AmarS03/Tiny-Parking-System/3d-print-model/images/3.png

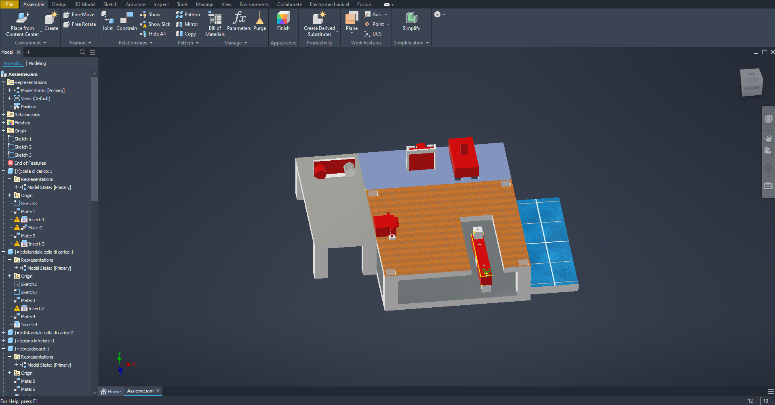
3d-print-model/images/3.png
