AmarS03/Tiny-Parking-System/esp/components/ultrasonic_sensor/ultrasonic_sensor.h

/**
 * @file ultrasonic.h
 * 
 * Header file for the ultrasonic sensor interface module
 * 
 */

#ifndef ULTRASONIC_SENSOR_H
#define ULTRASONIC_SENSOR_H

#include "esp_err.h"
#include <stdbool.h>

esp_err_t ultrasonic_sensor_init();

bool ultrasonic_sensor_detect();

#endif /* ULTRASONIC_SENSOR_H */
