AmarS03/Tiny-Parking-System/esp/main/fsm.c

/*
 * fsm.c
 *
 * Function definitions for the various states of the system
 *
 */

#include "fsm.h"
#include "freertos/FreeRTOS.h"
#include "freertos/task.h"
#include "freertos/event_groups.h"
#include "driver/gpio.h"
#include "ultrasonic.h"
#include "esp_wifi.h"
#include "esp_event.h"
#include "esp_log.h"
#include "esp_system.h"
#include "esp_sleep.h"

#include <stdbool.h>

#include "../components/cv/cv.h"
#include "../components/weight/weight.h"
#include "../components/ultrasonic_sensor/ultrasonic_sensor.h"
#include "../components/https/https.h"
#include "../components/https/https_task.h"
#include "../components/init/init.h"
#include "../components/servo_motor/servo_motor.h"
#include "../components/oled/oled.h"

// Idle delay function for low power mode
#ifdef CONFIG_USE_MOCK_CAMERA
    #define IDLE_DELAY() vTaskDelay(pdMS_TO_TICKS(200))
#else
    #define IDLE_DELAY() do { \
        esp_sleep_enable_timer_wakeup(200000); \
        esp_light_sleep_start(); \
    } while(0)
#endif

#define TOTAL_PARKING_SPOTS 10

// Current state of the FSM
static State_t curr_state = INIT;

// Flag that avoids multiple concurrent recognitions
static bool recognition_busy = false;

// Parking spot counter
static int parking_spots_available = TOTAL_PARKING_SPOTS;

// Prototypes of state functions
static void init_fn();

static void idle_fn();

static void entry_fn();

static void refuse_fn();

static void allow_fn();

static void exit_fn();


////////////////////////////////////////////////////////////////
//////////////// FSM Logic /////////////////////////////////////
////////////////////////////////////////////////////////////////

void fsm_handle_event(Event_t event) {
    switch (curr_state) {
        case IDLE:
            if (event == VALID_WEIGHT_DETECTED) {
                curr_state = VEHICLE_ENTRY;
            } else if (event == EXIT_DETECTED) {
                curr_state = VEHICLE_EXIT;
            } else if (event == REMOTE_OPEN) {
                curr_state = ENTRY_ALLOWED;
            }
            break;
        case VEHICLE_ENTRY:
            if (event == PLATE_RECOGNIZED) {
                curr_state = ENTRY_ALLOWED;
            } else if (event == PLATE_REFUSED) {
                curr_state = ENTRY_REFUSED;
            }
            break;
        default:
            // Handle invalid state
        break;
    }

}

void fsm_run_state_function() {
    switch (curr_state) {
        case INIT:
            init_fn();
            break;
        case IDLE:
            idle_fn();
            break;
        case VEHICLE_ENTRY:
            entry_fn();
            break;
        case ENTRY_REFUSED:
            refuse_fn();
            break;
        case ENTRY_ALLOWED:
            allow_fn();
            break;
        case VEHICLE_EXIT:
            exit_fn();
            break;
        default:
            // Handle invalid state
            break;
    }
}

////////////////////////////////////////////////////////////////
//////////////// FSM State Functions ///////////////////////////
////////////////////////////////////////////////////////////////

/**
 * Initializes the whole system
 */
void init_fn() {
    system_init();

    #ifdef CONFIG_USE_MOCK_CAMERA
    ESP_LOGI("IDLE", "Running in MOCK CAMERA mode (Wokwi simulation)");
    #endif

    ESP_LOGI("INIT", "System ready. Waiting for detection...");

    vTaskDelay(pdMS_TO_TICKS(2000));

    ESP_LOGI("INIT", "Displaying status on OLED...");


    oled_print(0, "ESP32-S3 READY");
    oled_print(2, "HX711 OK");
    oled_print(4, "WiFi CONNECTED");

    vTaskDelay(pdMS_TO_TICKS(5000));

    oled_clear();

    curr_state = IDLE;
}

/**
 * When in idle state, the system enters low
 * power mode and waits for interrupts
 */
void idle_fn() {
    // System waiting for an event
    oled_clear();

    if (parking_spots_available <= 0) {
        enable_weight_detection(false);
        oled_print(2, "The parking lot");
        oled_print(4, "is full!");
    } else {
        enable_weight_detection(true);
        recognition_busy = false;
        char spots_str[20];
        snprintf(spots_str, sizeof(spots_str), "%d parking spots", parking_spots_available);
        oled_print(2, spots_str);
        oled_print(4, "available");
    }

    // Enter low power mode
    IDLE_DELAY();

    // wait for the ultrasonic sensor to detect vehicle passage
    if (ultrasonic_sensor_detect()) {
        ESP_LOGI("IDLE", "Detected vehicle exiting...");
        vTaskDelay(pdMS_TO_TICKS(500)); // Debounce delay
        fsm_handle_event(EXIT_DETECTED);
    }
}

/**
 * Detects weight and runs the CV algorithm.
 * Decide whether to allow or refuse entrance
 */
void entry_fn() {
    enable_weight_detection(false);

    oled_clear();

    oled_print(2, "Verifying license");
    oled_print(4, "plate...");

    if (!recognition_busy) {
        unblock_recognition_task();
        recognition_busy = true;
    }

    vTaskDelay(pdMS_TO_TICKS(2000));

    oled_clear();
}

/**
 * Shows a negative message
 * on the display
 */
void refuse_fn() {
    oled_clear();
    ESP_LOGI("REFUSE", "Entry refused. Access denied.");

    oled_print(2, "Your vehicle");
    oled_print(4, "is not allowed!");

    vTaskDelay(pdMS_TO_TICKS(5000));

    oled_clear();
    curr_state = IDLE;
}

/**
 * Shows a positive message on the
 * display, opens the gate bar and waits a signal
 * from the ultrasonic sensor to close it again
 */
void allow_fn() {
    oled_clear();
    ESP_LOGI("ALLOW", "Entry allowed. Opening gate...");

    oled_print(3, "Entrance allowed!");

    // Update counter
    parking_spots_available -= (parking_spots_available > 1) ? 1 : 0;

    // raise the barrier when entry is allowed
    servo_motor_raise_barrier();

    // wait for the ultrasonic sensor to detect vehicle passage
    bool is_still_detecting = false;

    // Await vehicle passage
    while (!is_still_detecting) {
        is_still_detecting = ultrasonic_sensor_detect();
        vTaskDelay(pdMS_TO_TICKS(200));
    }

    ESP_LOGI("ALLOW", "Vehicle passing the gate...");

    // Await vehicle clearance
    while (is_still_detecting) {
        is_still_detecting = ultrasonic_sensor_detect();
        vTaskDelay(pdMS_TO_TICKS(200));
    }

    ESP_LOGI("ALLOW", "Vehicle passed. Closing gate...");

    oled_clear();

    oled_print(3, "Closing gate...");
    
    // close the barrier after ultrasonic read
    servo_motor_lower_barrier();
    vTaskDelay(pdMS_TO_TICKS(3000));
    
    oled_clear();
    curr_state = IDLE;
}

/**
 * Opens the gate bar for exit
 * and waits for the vehicle to leave
 */
void exit_fn() {
    oled_clear();
    enable_weight_detection(false);
    ESP_LOGI("EXIT", "Exit allowed. Opening gate...");

    oled_print(3, "Vehicle exiting");

    // Update counter
    parking_spots_available += (parking_spots_available < TOTAL_PARKING_SPOTS) ? 1 : 0;

    // Raise the barrier when vehicle exit is detected
    servo_motor_raise_barrier();

    // Wait for some time to allow vehicle to exit
    vTaskDelay(pdMS_TO_TICKS(5000));

    // Close the barrier after delay
    servo_motor_lower_barrier();
    
    ESP_LOGI("EXIT", "Vehicle passed. Closing gate...");

    // Send exit notification to backend
    set_license_plate_data("invalid_plate");
    xTaskCreate(post_exit_task, "post_exit_task", 8192, NULL, 5, NULL);
    vTaskDelay(pdMS_TO_TICKS(5000));

    oled_clear();
    
    curr_state = IDLE;
}
