AmarS03/Tiny-Parking-System/esp/main/init.h

/**
 * @file init.h
 * 
 * Initilization functions header file
 * 
 */



#ifndef INIT_H
#define INIT_H

void hw_init();

void camera_init();

void ultrasonic_sensor_init();

void weight_sensor_init();

void wifi_init();


#endif /* INIT_H */
